diglet48/FOC-Stim/docs/images/42tl004-saturation.png

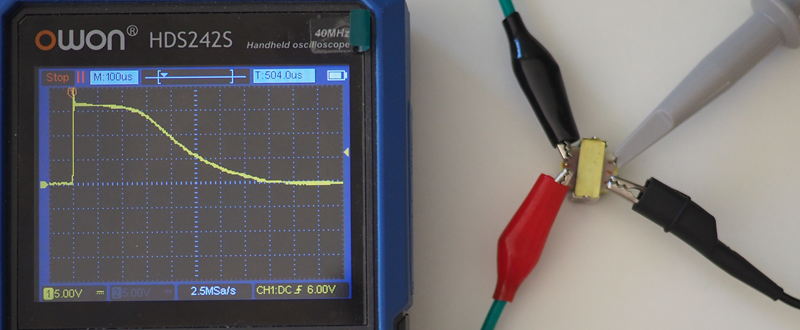
docs/images/42tl004-saturation.png
