diglet48/FOC-Stim/src/bsp/config_g431b_esc1.h

#if defined(ARDUINO_B_G431B_ESC1)
#ifndef FOCSTIM_CONFIG_G431B_ESC1_H
#define FOCSTIM_CONFIG_G431B_ESC1_H

#include "../signals/transformers.h"
#include "../signals/output_stage.h"

// transformer and output stage specs
static constexpr OutputStage OUTPUT_STAGE = {
    .resistance = 0.5f,    // driver Rdson (0.03) + inductor DC resistance (0.2) + fudge factor.
    .inductance = 220e-6f, // µH
    .capacitance = 10e-6f, // µF
    .transformer = XICON_42TU200_MIDDLE_PIN,
};

// current limits
#define BODY_CURRENT_MAX  0.20f             // in amps, body current
#define ESTOP_CURRENT_LIMIT_MARGIN 0.3f     // accounts for measurement noise, driving current

// board temperature limits
#define MAXIMUM_TEMPERATURE 100.f    // degrees celsius.

// supply voltage
#define STIM_STATIC_VOLTAGE
#define STIM_PSU_VOLTAGE 12.0f
#define STIM_PSU_VOLTAGE_MIN 11.0f // e-stop if exceeded
#define STIM_PSU_VOLTAGE_MAX 15.0f // e-stop if exceeded

// pwm
#define STIM_PWM_FREQ 50000 // switching frequency is twice this frequency
#define STIM_PWM_MINIMUM_OFF_TIME 3e-6f // limited by pwm-rejection of current sense. Experimentally determined to be 2.6us.
#define STIM_PWM_MAX_DUTY_CYCLE float(1 - STIM_PWM_MINIMUM_OFF_TIME * STIM_PWM_FREQ)
#define STIM_PWM_MAX_VDRIVE (STIM_PWM_MAX_DUTY_CYCLE * STIM_PSU_VOLTAGE)

// potentiometer volume control
#define POTMETER_ZERO_PERCENT_VALUE      4096.f
#define POTMETER_HUNDRED_PERCENT_VALUE   0.0f

// initial conditions and limits for the model
#define MODEL_RESISTANCE_INIT (200.f / STIM_WINDING_RATIO_SQ)
#define MODEL_IMPEDANCE_INIT {1, 1}
#define MODEL_RESISTANCE_MIN .7f
#define MODEL_RESISTANCE_MAX 15.f
#define MODEL_PHASE_ANGLE_MIN -1.5f
#define MODEL_PHASE_ANGLE_MAX 1.5f

// transformer saturation
#define MODEL_FIXED_RESISTANCE      1.0f        // driver Rdson + low pass filter + transformer low-side resistance
#define MODEL_MAXIMUM_VOLT_SECONDS  3600e-6f    // Xicon 42TU200

// enable for nicer looking waveforms on the scope. Not safe for humans!
// #define THREEPHASE_PULSE_DEFEAT_RANDOMIZATION

#define CURRENT_SENSE_SCALE_FULL

#endif // FOCSTIM_CONFIG_G431B_ESC1_H
#endif
