diglet48/FOC-Stim/src/bsp/config_version.h

#ifndef FOCSTIM_CONFIG_VERSION_H
#define FOCSTIM_CONFIG_VERSION_H

constexpr int focstim_api_version_major = 1;
constexpr int focstim_api_version_minor = 3;
constexpr int focstim_api_version_revision = 2;
static constexpr char focstim_api_branch_name[] = "main";   // mainline restim requires this to be "main".
static constexpr char focstim_api_comment[] = "";           // can be whatever.

#endif
