diglet48/FOC-Stim/src/sensors/as5311.h

#ifndef FOCSTIM_AS5311_H
#define FOCSTIM_AS5311_H

#include "stim_clock.h"

// pins for V4
#define PORT_DO GPIOC
#define PIN_DO  LL_GPIO_PIN_4
#define PORT_CSN GPIOC
#define PIN_CSN LL_GPIO_PIN_5
#define PORT_CLK GPIOB
#define PIN_CLK LL_GPIO_PIN_0


#define FLAG_OCF_MASK (1 << 5)  // offset compensation.
#define FLAG_COF_MASK (1 << 4)  // cordic overflow
#define FLAG_LIN_MASK (1 << 3)
#define FLAG_INC_MASK (1 << 2)
#define FLAG_DEC_MASK (1 << 1)
#define FLAG_PAR_MASK (1 << 0)  // parity

class AS5311 {
    public:

    void init(float read_interval_s, float notification_interval_s);
    void update();

private:
    void read_sensor();
    void transmit_sensor_position();


    Clock read_clock;
    Clock notification_clock;
    float read_interval_s;
    float notification_interval_s;

    bool is_sensor_detected;
    int last_raw;
    int position;
    int flags;
};

#endif
