diglet48/FOC-Stim/src/utils.cpp

#include <cmath>

#include "utils.h"
#include "foc_utils.h"
#include <algorithm>

float float_rand(float min, float max)
{
    float scale = rand() / (float)RAND_MAX; /* [0, 1.0] */
    return min + scale * (max - min);       /* [min, max] */
};

float norm(float x, float y)
{
    return sqrtf(x * x + y * y);
}

float lerp(float p, float a, float b)
{
    return a + std::min(1.0f, std::max(0.0f, p)) * (b - a);
}

float interpolate(
    float x,
    float x0, float x1,
    float y0, float y1)
{
    if (x1 == x0)  // prevent divide-by-zero
        return y0;

    float p = std::clamp((x - x0) / (x1 - x0), 0.f, 1.f);
    return y0 + p * (y1 - y0);
}

float inverse_lerp(float v, float a, float b)
{
    float p = (a - v) / (a - b);
    return std::clamp<float>(p, 0.f, 1.f);
}

float ntc_voltage_to_temp(float ADCVoltage)
{
    // Formula: https://www.giangrandi.org/electronics/ntc/ntc.shtml
    const float ResistorBalance = 4700.0;
    const float Beta = 3425.0f;
    const float RoomTempI = 1.0F / 298.15f; //[K]
    const float Rt = ResistorBalance * ((3.3F / ADCVoltage) - 1);
    const float R25 = 10000.0F;

    float T = 1.0f / ((logf(Rt / R25) / Beta) + RoomTempI);
    T = T - 273.15f;

    return T;
}
